Jana-Marie/otterlinear-keyboard/tooling/gif/frame00000.png

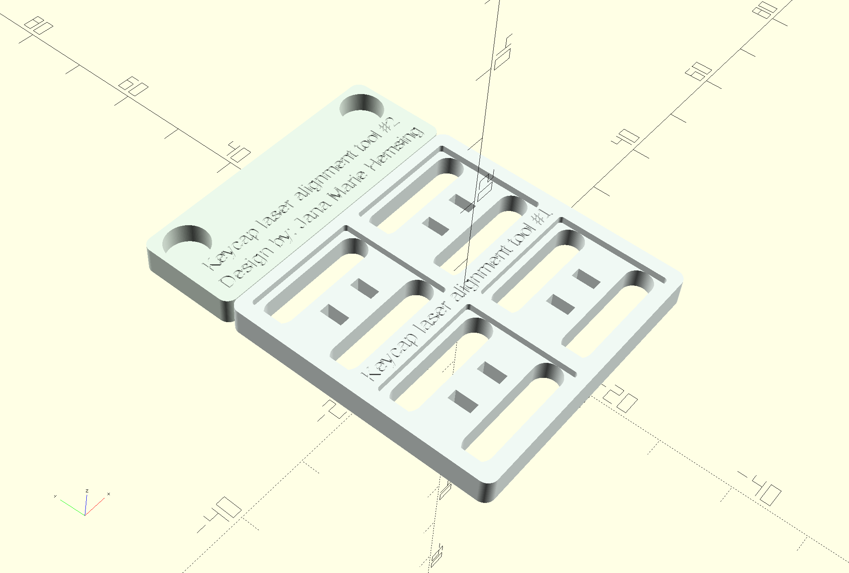
tooling/gif/frame00000.png
