Jana-Marie/otterlinear-keyboard/tooling/gif/frame00017.png

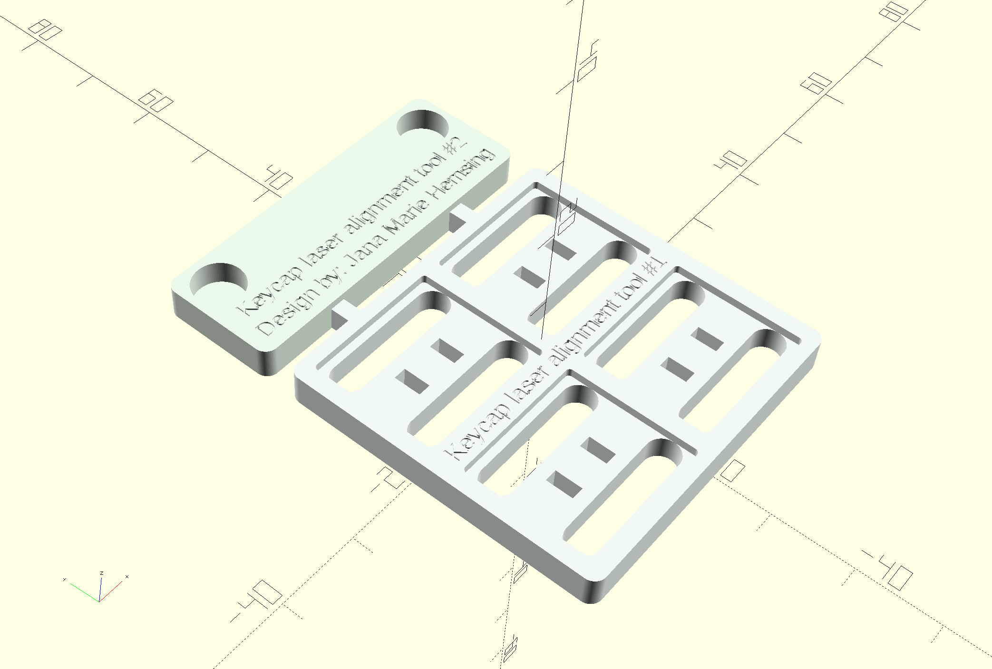
tooling/gif/frame00017.png
