Jana-Marie/otterlinear-keyboard/tooling/gif/frame00026.png

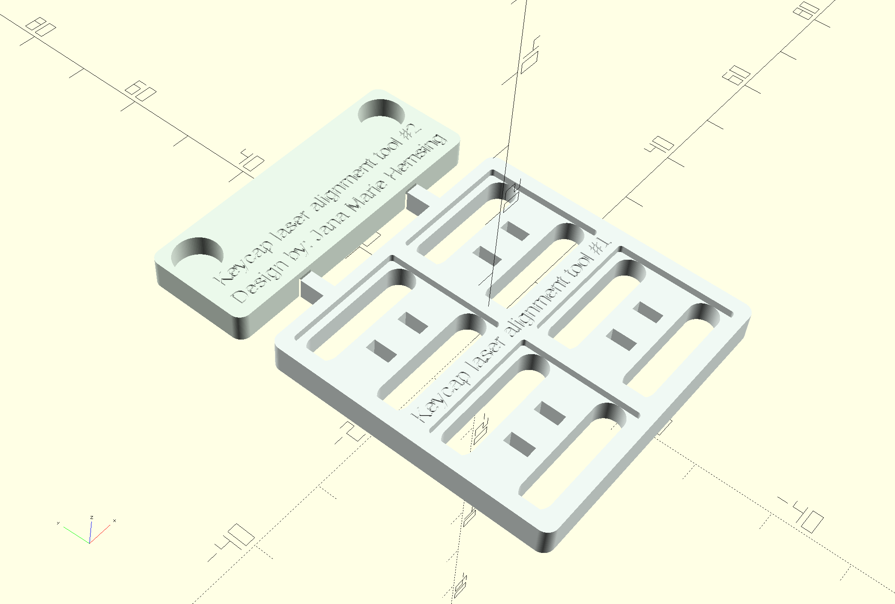
tooling/gif/frame00026.png
