Jana-Marie/otterlinear-keyboard/tooling/gif/frame00037.png

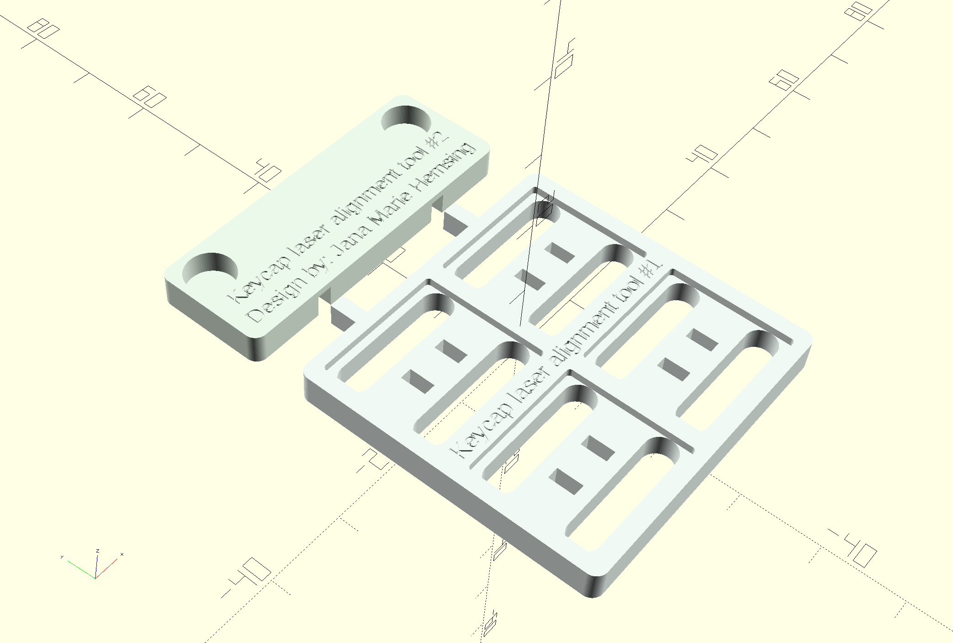
tooling/gif/frame00037.png
