Jana-Marie/otterlinear-keyboard/firmware/Core/Src/mapping.c

#include <stdint.h>

uint8_t layer_0[5][12] = {
  {0x00,0x00,0x85,0x00,0x2c,0x2c,0x2c,0x00,0x00,0x50,0x51,0x4f},
  {0x00,0x1d,0x1b,0x06,0x19,0x05,0x11,0x10,0x36,0x37,0x52,0x38},
  {0x00,0x04,0x16,0x07,0x09,0x0a,0x0b,0x0d,0x0e,0x0f,0x33,0x28},
  {0x2b,0x14,0x1a,0x08,0x15,0x17,0x1c,0x18,0x0c,0x12,0x13,0x2a},
  {0x29,0x1e,0x1f,0x20,0x21,0x22,0x23,0x24,0x25,0x26,0x27,0x4c}
};

//uint8_t layer_0[5][12] = {
//  {,,,,,,,,,,,},
//  {,,,,,,,,,,,},
//  {,,,,,,,,,,,},
//  {,,,,,,,,,,,},
//  {,,,,,,,,,,,}
//};
